Cristian-Ariel/keyless-motorcycle-igntion-with-a-ring-nfc/source code/keyless_motorcycle_ignition_v1.0/soundsList.h

void PlayPreTone(const byte tonePin)
{
  tone(tonePin, 2900, 34);
  delay(90);
  tone(tonePin, 2900, 34);
  delay(600);  // A small delay so the sound doesn't overlap other sounds
}

void PlayAcceptedTag(const byte tonePin)
{
  tone(tonePin, 2900, 105);
  delay(100);
  tone(tonePin, 1700, 84);
  delay(200);
  tone(tonePin, 1700, 94);
  delay(594);
}

void PlayUnknwownTag(const byte tonePin)
{
  tone(tonePin, 112, 140);
  delay(260);
  tone(tonePin, 109, 146);
  delay(73);
  tone(tonePin, 110, 126);
  delay(94);
  tone(tonePin, 110, 108);
  delay(194);
  tone(tonePin, 110, 630); // Simultates a "warning" tone
  delay(1000);
}

void PlayEnterSaveDeleteTagMode(const byte tonePin)
{
  tone(tonePin, 1150, 84);
  delay(90);
  tone(tonePin, 1450, 84);
  delay(90);
  tone(tonePin, 1700, 84);
  delay(200);
  tone(tonePin, 1900, 94);
  delay(195);
  tone(tonePin, 2800, 105);
  delay(105);
}

void PlayExitSaveDeleteTagMode(const byte tonePin)
{
  tone(tonePin, 2800, 105);
  delay(105);
  tone(tonePin, 1900, 94);
  delay(195);
  tone(tonePin, 1700, 84);
  delay(200);
  tone(tonePin, 1450, 84);
  delay(90);
  tone(tonePin, 1150, 84);
  delay(500);
}

void PlayEnterEraseMemoryMode(const byte tonePin)
{
  tone(tonePin, 880, 8);
  delay(9);
  tone(tonePin, 2349, 95);
  delay(106);
  tone(tonePin, 1318, 43);
  delay(48);
  tone(tonePin, 880, 8);
  delay(9);
  tone(tonePin, 2349, 95);
  delay(106);
  tone(tonePin, 1318, 43);
  delay(48);
  tone(tonePin, 880, 8);
  delay(9);
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
  tone(tonePin, 112, 630); // Simultates a "warning" tone
  delay(290);
  tone(tonePin, 75, 930);  // Simultates a "warning" tone
  delay(1200);
}

void PlayReaderNotFound(const byte tonePin)
{
  tone(tonePin, 2070, 1500); 
  delay(2000);
  tone(tonePin, 132, 1800); 
  delay(1800);
}
